Akrobate/round-timer/3D-model/components/lampComponent.scad

use <../pieces/lampshadeHolderPiece.scad>
use <../pieces/lampshadePiece.scad>
use <../pieces/boltJoinPiece.scad>
use <../openscad_modules/led/ledWS2812/ledWS2812.scad>

include <../configurations/global.scad>


/**
 * lampComponent
 * @name lampComponent
 * @description lampComponent
 * @type component
 */
module lampComponent() {

    translate([0, 0, boltJoinPiece_height])
        ledWS2812Grid();

    boltJoinPiece();
    
    color("DarkSlateGray")
        lampshadeHolderPiece();

    color("PaleTurquoise", alpha = 0.5)
        lampshadePiece();
}


/**
 * @png
 * @colorscheme BeforeDawn
 */
lampComponent();
