Akrobate/round-timer/3D-model/configurations/global.scad

space_between_lamps = 85;


lampshade_piece_lampshade_diameter = 60;
lampshade_piece_lampshade_height = 70;
lampshade_piece_walled_width = 1;
lampshade_piece_border_diameter = 64;
lampshade_piece_border_height = 2;


lampshade_holder_piece_holder_external_diameter = 75;
lampshade_holder_piece_lampshade_diameter = 61;
lampshade_holder_piece_lampshade_border_diameter = 65;
lampshade_holder_piece_lampshade_border_height = 2.1;
lampshade_holder_piece_holder_height = 4;
lampshade_holder_piece_bolt_throws_count = 4;
lampshade_holder_piece_bolt_throws_diameter = 3.5;
lampshade_holder_piece_bolt_throws_z = 4;

case_external_panes_thickness = 4.8;

external_size = [265, 95, 60];

angleHolderPiece_size_x = 25;
angleHolderPiece_size_y = 25;
angleHolderPiece_size_z = 8;

angleHolderPiece_insert_generic_offset = 10;
angleHolderPiece_insert_z_offset_x = angleHolderPiece_insert_generic_offset;
angleHolderPiece_insert_z_offset_y = angleHolderPiece_insert_generic_offset;
angleHolderPiece_insert_x_offset = angleHolderPiece_insert_generic_offset;
angleHolderPiece_insert_y_offset = angleHolderPiece_insert_generic_offset;
    
throw_diameter = 3;



buttonHolderPiece_size = [30, 30, 2];
buttonHolderPiece_border_radius = 4;

buttonHolderPiece_throws_diameter = 3.5;
buttonHolderPiece_throws_margin = 4;

buttonHolderPiece_button_diameter = 19.5;
buttonHolderPiece_clips_button_diameter = 20.64;
buttonHolderPiece_clips_button_thickness = 4;
buttonHolderPiece_foolproof_button_diameter = 20.34;
buttonHolderPiece_foolproof_button_thickness = 2;

buttonHolderPiece_correction_button_diameter = 0.5;
buttonHolderPiece_correction_clips_button_diameter = 0.5;
buttonHolderPiece_correction_clips_button_thickness = 0.5;
buttonHolderPiece_correction_foolproof_button_diameter = 0.5;
buttonHolderPiece_correction_foolproof_button_thickness = 0.5;

buttonHolderPiece_fn = 500;

buttonFixationThrows_correction_button_diameter = 0.5;


beeperHolder_size = [30, 20, 2];

beeperHolder_buzzer_diameter = 12.5;
beeperHolder_buzzer_border_holder = 2;
beeperHolder_buzzer_holder_height = 4;


boltJoinPiece_internal_diameter = 3.5;
boltJoinPiece_external_diameter = 3.5 + (0.4 * 2);
boltJoinPiece_height = 3;

topPanePiece_cable_throw_margin = 10;
